JackiePease/QuipuColumn/3D_printing_and_laser_cutting_files/for_50mm_pipe/corner.stl

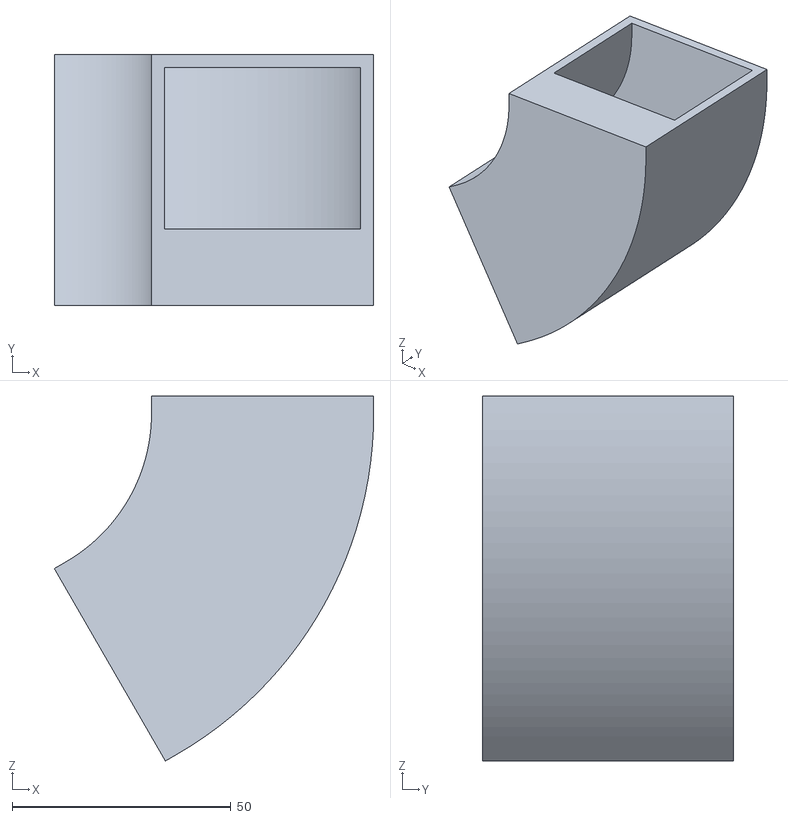
[picture p27: CAD file, 2026-05-02]
3D_printing_and_laser_cutting_files/for_50mm_pipe/corner.stl
73.0 x 57.5 x 83.4
